jay94ks/simple-np/fw/kbd/handlers/numlock.cpp

#include "numlock.h"
#ifdef __INTELLISENSE__
#include "../../tusb_config.h"
#endif
#include "../../board/config.h"
#include "../../board/ledctl.h"
#include "../../tft/tft.h"
#include <tusb.h>

KbdNumlockHandler* KbdNumlockHandler::instance() {
    static KbdNumlockHandler _handler;
    return &_handler;
}

bool KbdNumlockHandler::onKeyUpdated(Kbd* kbd, EKey key, EKeyState state) {
    if (key != EKEY_NUMLOCK) {
        switch(key) {
            case EKEY_NUM_0:
            case EKEY_NUM_1:
            case EKEY_NUM_2:
            case EKEY_NUM_3:
            case EKEY_NUM_4:
            case EKEY_NUM_5:
            case EKEY_NUM_6:
            case EKEY_NUM_7:
            case EKEY_NUM_8:
            case EKEY_NUM_9:
                return true;

            default:
                break;
        }
        return false;
    }
    
    SKey* numlock = kbd->getKeyPtr(key);
    switch(state) {
        case EKLS_RISE: // --> updating on `RELEASING` state.
            numlock->ts = ~numlock->ts;
            break;

        default:
            break;
    }

    // --> successfully handled.
    return true;
}

void KbdNumlockHandler::onKeyNotify(const Kbd* kbd, EKey key, EKeyState state) {
    if (key != EKEY_NUMLOCK) {
        return;
    }
    
    // --> apply toggle state.
    SKey* numlock = kbd->getKeyPtr(key);
    Ledctl::get()->set(ELED_NUMLOCK, numlock->ts);
    
    if (state == EKLS_FALL) {
        if (numlock->ts) {
            tty_print("[NUMLOCK] ON\n");
        } else {
            tty_print("[NUMLOCK] OFF\n");
        }
    }
}

CFG_TUD_EXTERN void tud_hid_set_report_cb(uint8_t instance, uint8_t report_id, hid_report_type_t report_type, uint8_t const* buffer, uint16_t bufsize) {
  (void) instance;

    if (report_type == HID_REPORT_TYPE_OUTPUT && report_id == RID_KEYBOARD) {
        if (bufsize < 1) {
            return;
        }

        Kbd* kbd = Kbd::get();
        SKey* numlock = kbd->getKeyPtr(EKEY_NUMLOCK);
        if (numlock == nullptr) {
            return;
        }

        // --> receive keyboard LED status.
        const uint8_t kbd_leds = buffer[0];

        // --> set the received toggle state.
        if ((kbd_leds & KEYBOARD_LED_NUMLOCK) != 0) {
            numlock->ts = 0xff;
        }

        else {
            numlock->ts = 0x00;
        }
        
        KbdNumlockHandler::instance()
            ->onKeyNotify(kbd, EKEY_NUMLOCK, EKLS_LOW);
    }
}

CFG_TUD_EXTERN uint16_t tud_hid_get_report_cb(uint8_t instance, uint8_t report_id, hid_report_type_t report_type, uint8_t* buffer, uint16_t reqlen) {
  (void) instance;
  (void) report_id;
  (void) report_type;
  (void) buffer;
  (void) reqlen;
  return 0;
}
